Sergiogargar/X4C-Moscatel/codeina/train_digital_twin/main/data_types.h

#ifndef DATA_TYPES_H
#define DATA_TYPES_H

#include <stdint.h>
#include "freertos/FreeRTOS.h"
#include "freertos/queue.h"
#include "freertos/semphr.h"

// Definiciones de la FFT y muestreo
#define FFT_SAMPLES 1024
#define FFT_RESOLUTION (FFT_SAMPLES / 2)

// Estructura para telemetría continua (GPS e IMU)
typedef struct {
    uint64_t timestamp_ms; // Unix timestamp en ms o uptime del sistema
    double latitude;
    double longitude;
    float altitude;
    float accel_x;
    float accel_y;
    float accel_z;
    float gyro_x;
    float gyro_y;
    float gyro_z;
    bool gps_valid;
    float dominant_freq_hz; // Frecuencia de mayor energía en el espectro FFT (Hz)
    float vibration_amplitude; // Amplitud máxima de vibración (Z-axis en dB)
} TelemetryData_t;

// Estructura con datos listos para enviar a SD y Red
typedef struct {
    TelemetryData_t telemetry;          // Estado del tren en el momento del muestreo
    float fft_spectrum[FFT_RESOLUTION]; // Espectro de frecuencias (magnitudes)
    uint8_t ref_count;                  // Número de consumidores que aún retienen este slot
} ProcessedVibrationData_t;

// Elemento de cola. Usamos puntero para evitar copiar todo el array grande (Zero-Copy)
typedef struct {
    ProcessedVibrationData_t* data_ptr;
} VibrationMessage_t;

// --- Variables y Handles Globales de Sincronización ---

// Mutex para proteger la lectura/escritura de la telemetría actual
extern SemaphoreHandle_t xTelemetryMutex;

// Estructura global que mantiene la última telemetría leída
extern TelemetryData_t currentTelemetry;

// Colas de FreeRTOS para enrutar el dato procesado
extern QueueHandle_t xSdQueue;
extern QueueHandle_t xNetworkQueue;

// Pool de memoria para evitar mallocs y fragmentación
extern QueueHandle_t xVibrationDataPool;

// Libera una referencia del slot de pool. Cuando ref_count llega a 0, devuelve el slot.
// Usa GCC atomics (__atomic_sub_fetch) — seguros en SMP sin necesitar spinlock externo.
static inline void pool_release(ProcessedVibrationData_t **ppData) {
    uint8_t remaining = __atomic_sub_fetch(&(*ppData)->ref_count, 1, __ATOMIC_ACQ_REL);
    if (remaining == 0) {
        xQueueSend(xVibrationDataPool, ppData, 0);
    }
}

#endif // DATA_TYPES_H
