Sergiogargar/X4C-Moscatel/codeina/wifi_test/main.c

#include "freertos/FreeRTOS.h"
#include "freertos/task.h"
#include "freertos/event_groups.h"
#include "esp_wifi.h"
#include "esp_event.h"
#include "esp_log.h"
#include "nvs_flash.h"
#include "esp_netif.h"
#include <string.h>

static const char *TAG = "WIFI_TEST";

#define WIFI_SSID       "DIGIFIBRA-kd5t"
#define WIFI_PASS       "N9G6k5GuFSUK"
#define WIFI_MAXIMUM_RETRY 5

static EventGroupHandle_t s_wifi_event_group;
static const int WIFI_CONNECTED_BIT = BIT0;
static const int WIFI_FAIL_BIT      = BIT1;
static int s_retry_num = 0;

static void event_handler(void* arg, esp_event_base_t event_base,
                         int32_t event_id, void* event_data)
{
    if (event_base == WIFI_EVENT && event_id == WIFI_EVENT_STA_START) {
        esp_wifi_connect();
    } else if (event_base == WIFI_EVENT && event_id == WIFI_EVENT_STA_DISCONNECTED) {
        if (s_retry_num < WIFI_MAXIMUM_RETRY) {
            esp_wifi_connect();
            s_retry_num++;
            ESP_LOGI(TAG, "Retry to connect to the AP" );
        } else {
            xEventGroupSetBits(s_wifi_event_group, WIFI_FAIL_BIT);
        }
        ESP_LOGI(TAG,"connect to the AP fail");
    } else if (event_base == IP_EVENT && event_id == IP_EVENT_STA_GOT_IP) {
        ip_event_got_ip_t* event = (ip_event_got_ip_t*) event_data;
        ESP_LOGI(TAG, "Got IP:" IPSTR, IP2STR(&event->ip_info.ip));
        s_retry_num = 0;
        xEventGroupSetBits(s_wifi_event_group, WIFI_CONNECTED_BIT);
    }
}

void app_main(void)
{
    ESP_ERROR_CHECK(nvs_flash_init());
    ESP_ERROR_CHECK(esp_netif_init());
    ESP_ERROR_CHECK(esp_event_loop_create_default());
    esp_netif_create_default_wifi_sta();

    wifi_init_config_t cfg = WIFI_INIT_CONFIG_DEFAULT();
    ESP_ERROR_CHECK(esp_wifi_init(&cfg));

    s_wifi_event_group = xEventGroupCreate();
    ESP_ERROR_CHECK(esp_event_handler_instance_register(WIFI_EVENT,
                                                        ESP_EVENT_ANY_ID,
                                                        &event_handler,
                                                        NULL,
                                                        NULL));
    ESP_ERROR_CHECK(esp_event_handler_instance_register(IP_EVENT,
                                                        IP_EVENT_STA_GOT_IP,
                                                        &event_handler,
                                                        NULL,
                                                        NULL));

    wifi_config_t wifi_config = {
        .sta = {
            .ssid = WIFI_SSID,
            .password = WIFI_PASS,
            .threshold.authmode = WIFI_AUTH_WPA2_PSK,
        },
    };
    ESP_ERROR_CHECK(esp_wifi_set_mode(WIFI_MODE_STA));
    ESP_ERROR_CHECK(esp_wifi_set_config(WIFI_IF_STA, &wifi_config));
    ESP_ERROR_CHECK(esp_wifi_start());

    ESP_LOGI(TAG, "Wifi initialization finished. Waiting for connection...");
    EventBits_t bits = xEventGroupWaitBits(s_wifi_event_group,
                                           WIFI_CONNECTED_BIT | WIFI_FAIL_BIT,
                                           pdFALSE,
                                           pdFALSE,
                                           portMAX_DELAY);

    if (bits & WIFI_CONNECTED_BIT) {
        ESP_LOGI(TAG, "WiFi connected successfully");
    } else if (bits & WIFI_FAIL_BIT) {
        ESP_LOGI(TAG, "Failed to connect to WiFi SSID:%s", WIFI_SSID);
    } else {
        ESP_LOGE(TAG, "UNEXPECTED EVENT");
    }

    // Keep the task alive so we can see the log.
    while (1) {
        vTaskDelay(pdMS_TO_TICKS(10000));
    }
}
